Ishikishik/flightradardisplay/mapdata.cpp

#include "mapdata.hpp"

const int lines[NUM_LINES][4] = {
  {276, 0, 189, 0},
  {189, 0, 189, 19},
  {189, 19, 166, 52},
  {166, 52, 164, 62},
  {164, 62, 137, 76},
  {137, 76, 124, 93},
  {124, 93, 75, 109},
  {75, 109, 70, 116},
  {70, 116, 54, 112},
  {54, 112, 56, 101},
  {56, 101, 52, 102},
  {52, 102, 55, 105},
  {55, 105, 48, 103},
  {48, 103, 52, 98},
  {52, 98, 65, 95},
  {65, 95, 69, 87},
  {69, 87, 44, 93},
  {44, 93, 41, 99},
  {41, 99, 44, 113},
  {44, 113, 9, 144},
  {9, 144, 15, 155},
  {15, 155, 9, 154},
  {9, 154, 8, 159},
  {8, 159, 0, 161},
  {0, 161, 0, 239},
  {0, 239, 22, 220},
  {22, 220, 20, 216},
  {20, 216, 41, 206},
  {41, 206, 50, 208},
  {50, 208, 51, 203},
  {51, 203, 33, 194},
  {33, 194, 39, 182},
  {39, 182, 48, 178},
  {48, 178, 49, 191},
  {49, 191, 53, 192},
  {53, 192, 53, 185},
  {53, 185, 56, 189},
  {56, 189, 70, 190},
  {70, 190, 57, 197},
  {57, 197, 74, 193},
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
};
